SheldonPeters7/HomeOwl/Capstone Project Files/THE CODE/code integration without beeper.docx

#include <Wire.h>

#include <Adafruit_VL53L0X.h>

#include <IRremote.h>

/******************************* Pin Definitions ********************************/

// ToF XSHUT Pins

#define XSHUT_FAR_RIGHT 4

#define XSHUT_MID_RIGHT 5

#define XSHUT_MID_LEFT 6

#define XSHUT_FAR_LEFT 7

// Motor Control

const int leftencoderApin = 2;

const int leftencoderBpin = 3;

const int rightencoderApin = 18;

const int rightencoderBpin = 19;

const int leftdirpin = 11;

const int rightdirpin = 12;

const int leftpwmpin = 9;

const int rightpwmpin = 10;

// IR & LEDs

#define RED 30

#define GREEN 31

#define BLUE 32

const int receiver = 8; // IR receiver pin

// Sound & Motion

const int sensorAnalogPin = A0;

const int sensorDigitalPin = 28;

const int ledPin = LED_BUILTIN;

const int pirPin1 = 22;

const int pirPin2 = 23;

const int pirPin3 = 24;

const int pirPin4 = 25;

/***************************** Sensor Objects ***********************************/

Adafruit_VL53L0X loxFarRight = Adafruit_VL53L0X();

Adafruit_VL53L0X loxMidRight = Adafruit_VL53L0X();

Adafruit_VL53L0X loxMidLeft = Adafruit_VL53L0X();

Adafruit_VL53L0X loxFarLeft = Adafruit_VL53L0X();

IRrecv irrecv(receiver);

/***************************** Global Variables *********************************/

// MPU-9250 Configuration

const int MPU_ADDR = 0x68;

const float GYRO_SCALE = 131.0; // ±250°/s range

float yaw = 0;

float gyroZOffset = 0;

unsigned long prevTime = 0;

// Motor Control

int leftencoderpulse = 0;

int rightencoderpulse = 0;

double ipr = 18.85; // inches per revolution

double tpr = 900; // ticks per revolution

int targetangle = 0;

int pwm = 100;

double error = 0, eI = 0, eD = 0, prev_error = 0;

const float Kp = 1.2, Ki = 0.3, Kd = 0;

float omega = 0, vL = 0, vR = 0;

const float wheelbase = 13.7; // inches

// System State

int ROBOT_STATE = 0; // 0=Off, 1=Standby, 2=Moving, 3=Searching

unsigned long stateStartTime = 0;

#define STANDBY_DURATION 3000

#define MOVING_DURATION 5000

#define SEARCHING_DURATION 5000

// Timing Intervals

unsigned long lastToFRead = 0;

unsigned long lastYawPrint = 0;

unsigned long lastNoiseTime = 0;

unsigned long lastMotionTime = 0;

const unsigned long yawPrintInterval = 1000;

const unsigned long noiseCooldown = 1000;

const unsigned long motionCooldown = 1000;

/********************************* Setup ***************************************/

void setup() {

Serial.begin(115200);

Wire.begin();

// Initialize MPU

Wire.beginTransmission(MPU_ADDR);

Wire.write(0x6B); // PWR_MGMT_1

Wire.write(0); // Wake up

Wire.endTransmission();

calibrateGyro();

// Initialize ToF sensors

pinMode(XSHUT_FAR_RIGHT, OUTPUT);

pinMode(XSHUT_MID_RIGHT, OUTPUT);

pinMode(XSHUT_MID_LEFT, OUTPUT);

pinMode(XSHUT_FAR_LEFT, OUTPUT);

initializeSensor(loxFarRight, XSHUT_FAR_RIGHT, 0x30, "Far Right");

initializeSensor(loxMidRight, XSHUT_MID_RIGHT, 0x31, "Middle Right");

initializeSensor(loxMidLeft, XSHUT_MID_LEFT, 0x32, "Middle Left");

initializeSensor(loxFarLeft, XSHUT_FAR_LEFT, 0x33, "Far Left");

// Motor Control Initialization

pinMode(leftencoderApin, INPUT);

pinMode(leftencoderBpin, INPUT);

attachInterrupt(digitalPinToInterrupt(leftencoderApin), ALeadingLeft, RISING);

attachInterrupt(digitalPinToInterrupt(leftencoderBpin), BLeadingLeft, RISING);

attachInterrupt(digitalPinToInterrupt(rightencoderApin), ALeadingRight, RISING);

attachInterrupt(digitalPinToInterrupt(rightencoderBpin), BLeadingRight, RISING);

pinMode(leftdirpin, OUTPUT);

pinMode(rightdirpin, OUTPUT);

pinMode(leftpwmpin, OUTPUT);

pinMode(rightpwmpin, OUTPUT);

// IR & LED Initialization

pinMode(RED, OUTPUT);

pinMode(GREEN, OUTPUT);

pinMode(BLUE, OUTPUT);

setLedState(0);

irrecv.enableIRIn();

// Sound & Motion Initialization

pinMode(sensorDigitalPin, INPUT);

pinMode(ledPin, OUTPUT);

pinMode(pirPin1, INPUT);

pinMode(pirPin2, INPUT);

pinMode(pirPin3, INPUT);

pinMode(pirPin4, INPUT);

calibrateSensor();

Serial.println("System initialization complete!");

delay(2000); // Initial stabilization

}

/********************************* Main Loop ***********************************/

void loop() {

// Update sensor data

updateGyro();

checkSound();

checkMotion();

// Handle IR input

if (irrecv.decode()) {

translateIR();

irrecv.resume();

}

// State machine processing

processStateMachine();

// Handle periodic tasks

printYawIfNeeded();

readToFSensorsPeriodically();

}

/***************************** Core Functions **********************************/

void processStateMachine() {

if (ROBOT_STATE == 0) return;

unsigned long currentTime = millis();

unsigned long elapsedTime = currentTime - stateStartTime;

switch (ROBOT_STATE) {

case 1: // Standby

if (elapsedTime >= STANDBY_DURATION) {

setState(2);

}

break;

case 2: // Moving

computePID();

rotateRobotRight();

if (elapsedTime >= MOVING_DURATION) {

setState(3);

}

break;

case 3: // Searching

if (elapsedTime >= SEARCHING_DURATION) {

setState(2);

}

break;

}

}

void setState(int newState) {

ROBOT_STATE = newState;

stateStartTime = millis();

setLedState(ROBOT_STATE);

Serial.print("New state: ");

Serial.println(ROBOT_STATE);

}

/***************************** ToF Functions ***********************************/

void initializeSensor(Adafruit_VL53L0X &sensor, int xshutPin, uint8_t newAddress, const char* position) {

digitalWrite(xshutPin, LOW);

delay(10);

digitalWrite(xshutPin, HIGH);

delay(10);

if (!sensor.begin(newAddress)) {

Serial.print(position);

Serial.println(" sensor failed to boot!");

while(1);

}

Serial.print(position);

Serial.print(" sensor initialized at 0x");

Serial.println(newAddress, HEX);

}

void readSensor(Adafruit_VL53L0X &sensor, const char* position) {

VL53L0X_RangingMeasurementData_t measure;

sensor.rangingTest(&measure, false);

if(measure.RangeStatus != 4) {

Serial.print(position);

Serial.print(": ");

Serial.print(measure.RangeMilliMeter);

Serial.println(" mm");

} else {

Serial.print(position);

Serial.println(": Out of range");

}

}

void readAllToFSensors() {

readSensor(loxFarRight, "Far Right");

readSensor(loxMidRight, "Middle Right");

readSensor(loxMidLeft, "Middle Left");

readSensor(loxFarLeft, "Far Left");

}

void readToFSensorsPeriodically() {

if (millis() - lastToFRead >= 1000) {

readAllToFSensors();

lastToFRead = millis();

}

}

/***************************** MPU Functions ***********************************/

void updateGyro() {

int16_t rawGyroZ = readGyroZ();

float gyroZ = (rawGyroZ - gyroZOffset) / GYRO_SCALE;

unsigned long currentTime = micros();

float dt = (currentTime - prevTime) / 1000000.0;

prevTime = currentTime;

yaw += gyroZ * dt;

}

void printYawIfNeeded() {

if (millis() - lastYawPrint >= yawPrintInterval) {

Serial.print("Yaw: ");

Serial.println(yaw, 2);

lastYawPrint = millis();

}

}

void calibrateGyro() {

Serial.println("Calibrating gyro... Keep sensor stationary!");

delay(1000);

long total = 0;

for(int i = 0; i < 1000; i++) {

total += readGyroZ();

delay(1);

}

gyroZOffset = total / 1000.0;

Serial.print("Calibration offset: ");

Serial.println(gyroZOffset);

}

int16_t readGyroZ() {

Wire.beginTransmission(MPU_ADDR);

Wire.write(0x47); // GYRO_ZOUT_H

Wire.endTransmission(false);

Wire.requestFrom(MPU_ADDR, 2, true);

return Wire.read() << 8 | Wire.read();

}

/*************************** Sound/Motion Functions ****************************/

void calibrateSensor() {

long sum = 0;

for(int i = 0; i < 50; i++) sum += analogRead(sensorAnalogPin);

quietLevel = sum / 50;

loudNoiseThreshold = 400; // Hard-coded for testing

Serial.println("Sound sensor calibrated");

}

void checkSound() {

int analogValue = analogRead(sensorAnalogPin);

int digitalValue = digitalRead(sensorDigitalPin);

if((analogValue > loudNoiseThreshold) && (digitalValue == HIGH) &&

(millis() - lastNoiseTime > noiseCooldown)) {

handleNoiseDetection(analogValue);

triggerActionSound();

}

}

void handleNoiseDetection(int noiseLevel) {

lastNoiseTime = millis();

Serial.print("LOUD NOISE! Level: ");

Serial.println(noiseLevel);

for(int i = 0; i < 3; i++) {

digitalWrite(ledPin, HIGH);

delay(100);

digitalWrite(ledPin, LOW);

delay(100);

}

}

void triggerActionSound() {

Serial.println("Action: Sound detected!");

}

void checkMotion() {

if((digitalRead(pirPin1) || digitalRead(pirPin2) ||

digitalRead(pirPin3) || digitalRead(pirPin4)) &&

(millis() - lastMotionTime > motionCooldown)) {

handleMotionDetection();

}

}

void handleMotionDetection() {

lastMotionTime = millis();

Serial.println("Motion detected");

}

/***************************** Motor Functions *********************************/

void stopMotors() {

digitalWrite(leftdirpin, HIGH);

digitalWrite(rightdirpin, LOW);

analogWrite(leftpwmpin, 255);

analogWrite(rightpwmpin, 0);

}

// Encoder ISRs

void ALeadingLeft() {

if(digitalRead(leftencoderBpin) == LOW) leftencoderpulse--;

else leftencoderpulse++;

}

void BLeadingLeft() {

if(digitalRead(leftencoderApin) == LOW) leftencoderpulse++;

else leftencoderpulse--;

}

void ALeadingRight() {

if(digitalRead(rightencoderBpin) == LOW) rightencoderpulse++;

else rightencoderpulse--;

}

void BLeadingRight() {

if(digitalRead(rightencoderApin) == LOW) rightencoderpulse--;

else rightencoderpulse++;

}

void computePID() {

error = targetangle - yaw;

eI += error;

eD = prev_error - error;

prev_error = error;

if (eI > 200) eI = 0; // Anti-windup

omega = Kp * error + Ki * eI + Kd * eD;

omega = constrain(omega, 0, 100); // Limit output

}

void rotateRobotRight() {

vL = (omega * wheelbase) / 2;

vR = (omega * wheelbase) / 2;

if(targetangle > yaw) {

digitalWrite(leftdirpin, HIGH);

digitalWrite(rightdirpin, HIGH);

analogWrite(leftpwmpin, 255 - (vL * 0.152) - 45);

analogWrite(rightpwmpin, 255 - (vR * 0.152));

} else {

stopMotors();

}

}

/******************************* IR Functions **********************************/

void setLedState(int state) {

switch(state) {

case 0: // Off (Red)

digitalWrite(RED, HIGH); digitalWrite(GREEN, LOW); digitalWrite(BLUE, LOW);

break;

case 1: // Standby (Yellow)

digitalWrite(RED, HIGH); digitalWrite(GREEN, HIGH); digitalWrite(BLUE, LOW);

break;

case 2: // Moving (Green)

digitalWrite(RED, LOW); digitalWrite(GREEN, HIGH); digitalWrite(BLUE, LOW);

break;

case 3: // Searching (Cyan)

digitalWrite(RED, LOW); digitalWrite(GREEN, HIGH); digitalWrite(BLUE, HIGH);

break;

}

}

void translateIR() {

if (irrecv.decodedIRData.flags) {

irrecv.decodedIRData.decodedRawData = last_decodedRawData;

Serial.println("REPEAT!");

} else {

Serial.print("IR code:0x");

Serial.println(irrecv.decodedIRData.decodedRawData, HEX);

}

switch (irrecv.decodedIRData.decodedRawData) {

case 0xBA45FF00: // POWER

ROBOT_STATE = (ROBOT_STATE == 0) ? 1 : 0;

stateStartTime = millis();

setLedState(ROBOT_STATE);

break;

case 0xB847FF00: // FUNC/STOP

ROBOT_STATE = 1;

stateStartTime = millis();

setLedState(ROBOT_STATE);

break;

}

last_decodedRawData = irrecv.decodedIRData.decodedRawData;

delay(200);

}
