SheldonPeters7/HomeOwl/Capstone Project Files/THE CODE/IR-LED.docx

#include "IRremote.h"

// Define LED Pins

#define RED 30

#define GREEN 31

#define BLUE 32

int receiver = 8; // IR receiver pin

IRrecv irrecv(receiver);

uint32_t last_decodedRawData = 0;

int ROBOT_STATE = 0; // 0=Off, 1=Standby, 2=Moving, 3=Searching

unsigned long stateStartTime = 0;

void (*resetFunc)(void) = 0;

#define STANDBY_DURATION 3000

#define MOVING_DURATION 5000

#define SEARCHING_DURATION 5000

void setLedState(int state) {

switch(state) {

case 0: // Off (Red)

digitalWrite(RED, HIGH);

digitalWrite(GREEN, LOW);

digitalWrite(BLUE, LOW);

break;

case 1: // Standby (Yellow)

digitalWrite(RED, HIGH);

digitalWrite(GREEN, HIGH);

digitalWrite(BLUE, LOW);

break;

case 2: // Moving (Green)

digitalWrite(RED, LOW);

digitalWrite(GREEN, HIGH);

digitalWrite(BLUE, LOW);

break;

case 3: // Searching (Cyan)

digitalWrite(RED, LOW);

digitalWrite(GREEN, HIGH);

digitalWrite(BLUE, HIGH);

break;

}

}

void translateIR() {

if (irrecv.decodedIRData.flags) {

irrecv.decodedIRData.decodedRawData = last_decodedRawData;

Serial.println("REPEAT!");

} else {

Serial.print("IR code:0x");

Serial.println(irrecv.decodedIRData.decodedRawData, HEX);

}

switch (irrecv.decodedIRData.decodedRawData) {

case 0xBA45FF00: // POWER button

Serial.println("POWER");

if (ROBOT_STATE == 0) {

ROBOT_STATE = 1;

stateStartTime = millis();

setLedState(ROBOT_STATE);

} else {

ROBOT_STATE = 0;

setLedState(ROBOT_STATE);

}

Serial.print("New state: ");

Serial.println(ROBOT_STATE);

break;

case 0xB847FF00: // FUNC/STOP button (REPLACE THIS CODE WITH YOUR ACTUAL BUTTON'S HEX CODE)

Serial.println("FUNC/STOP");

ROBOT_STATE = 1; // Force standby state

stateStartTime = millis(); // Reset timer

setLedState(ROBOT_STATE);

Serial.print("New state: ");

Serial.println(ROBOT_STATE);

break;

default:

Serial.println("Unknown button");

}

last_decodedRawData = irrecv.decodedIRData.decodedRawData;

delay(200);

}

void setup() {

Serial.begin(9600);

pinMode(RED, OUTPUT);

pinMode(GREEN, OUTPUT);

pinMode(BLUE, OUTPUT);

setLedState(0);

Serial.println("IR Robot State Controller");

irrecv.enableIRIn();

}

void loop() {

if (irrecv.decode()) {

translateIR();

irrecv.resume();

}

if (ROBOT_STATE != 0) {

unsigned long currentTime = millis();

unsigned long elapsedTime = currentTime - stateStartTime;

switch (ROBOT_STATE) {

case 1: // Standby

if (elapsedTime >= STANDBY_DURATION) {

ROBOT_STATE = 2;

stateStartTime = currentTime;

setLedState(ROBOT_STATE);

Serial.print("New state: ");

Serial.println(ROBOT_STATE);

}

break;

case 2: // Moving

if (elapsedTime >= MOVING_DURATION) {

ROBOT_STATE = 3;

stateStartTime = currentTime;

setLedState(ROBOT_STATE);

Serial.print("New state: ");

Serial.println(ROBOT_STATE);

}

break;

case 3: // Searching

if (elapsedTime >= SEARCHING_DURATION) {

ROBOT_STATE = 2;

stateStartTime = currentTime;

setLedState(ROBOT_STATE);

Serial.print("New state: ");

Serial.println(ROBOT_STATE);

}

break;

}

}

}
