SheldonPeters7/HomeOwl/Capstone Project Files/Capstone Prep Work/Progress Presentations - Capstone Prep/prep Progress Presentation 2.pptx

## Home Owl Autonomous Security Robot

Samantha Buckle
Dylan Dauz
Sameeh Olipani
Sheldon Peters

## Project Recap

- This project aims to design and build a robot for use in the monitoring of indoor spaces
- Robot will be capable of:
  - Autonomous movement
  - Navigation of a building or room without the need for human control
  - Utilize sensors to detect loud noises or the presence of a person
  - Flash lights and play an alarm sound when disturbance is detected
  - Get signal from remote control to turn the system on and off

## Parts list

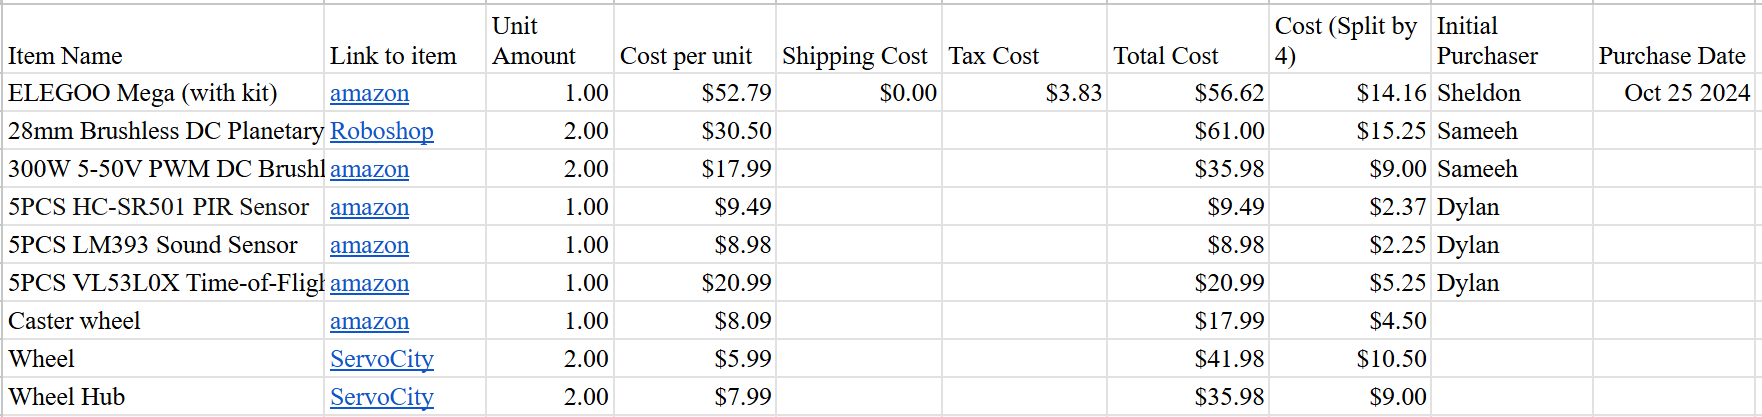
[picture p16: figure]

## Concept Design

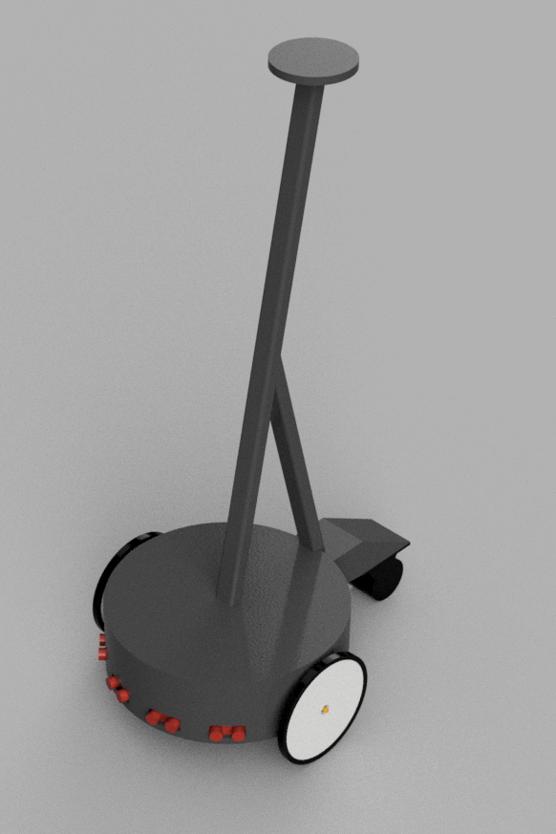
[picture p17: figure]

## Concept Design

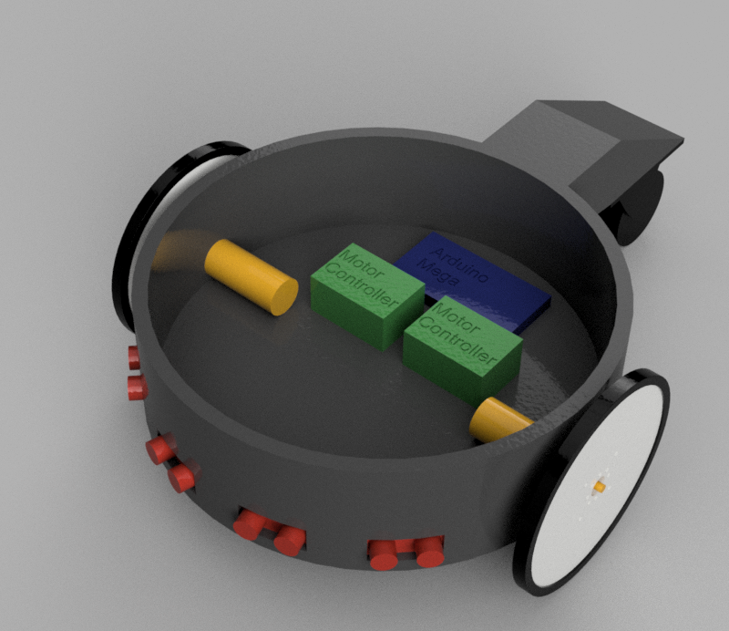
[picture p18: figure]

## Next Steps

- Order parts
- Safety trainings for lab access / 3D printing access
- Refine / finalize design
