SheldonPeters7/HomeOwl/Capstone Project Files/Fusion 360 files/Capstone 3D Models/Capstone/Rough Draft 2/Wheel.stl

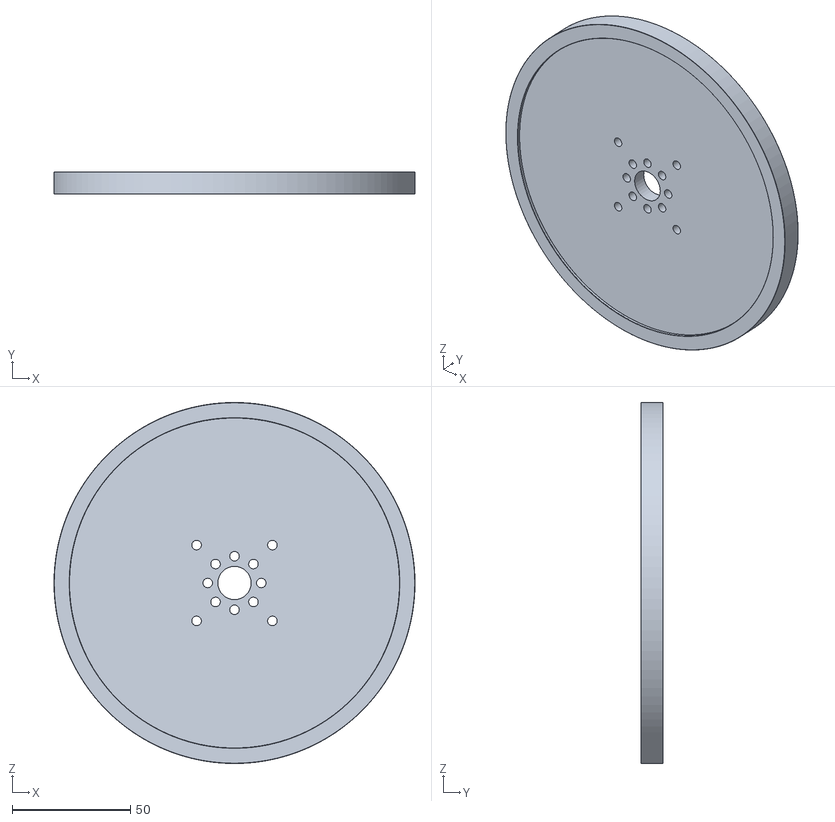
[picture p49: CAD file, 2025-04-22]
Capstone Project Files/Fusion 360 files/Capstone 3D Models/Capstone/Rough Draft 2/Wheel.stl
152.4 x 9.35 x 152.4
