SheldonPeters7/HomeOwl/Capstone Project Files/Fusion 360 files/Capstone 3D Models/Capstone/Rough Draft 2/Caster Wheel.stl

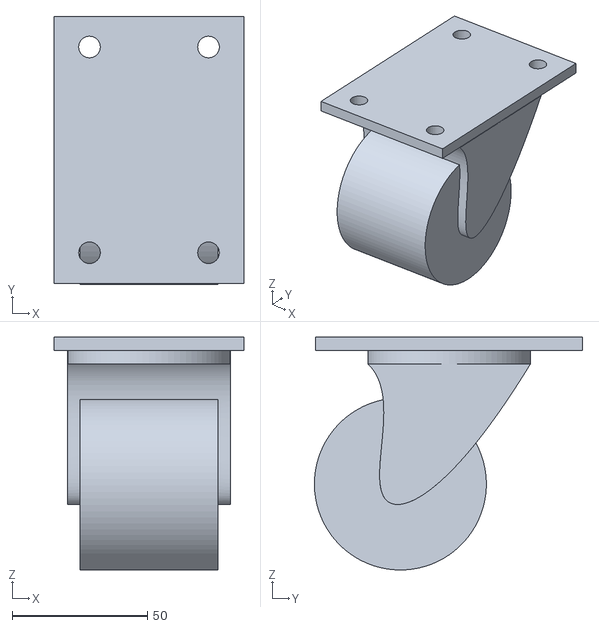
[picture p50: CAD file, 2025-04-22]
Capstone Project Files/Fusion 360 files/Capstone 3D Models/Capstone/Rough Draft 2/Caster Wheel.stl
70.1 x 99.0 x 86.0
