SheldonPeters7/HomeOwl/Capstone Project Files/Fusion 360 files/Capstone 3D Models/Capstone/Prototype/Arduino Mega Mount Plate.stl

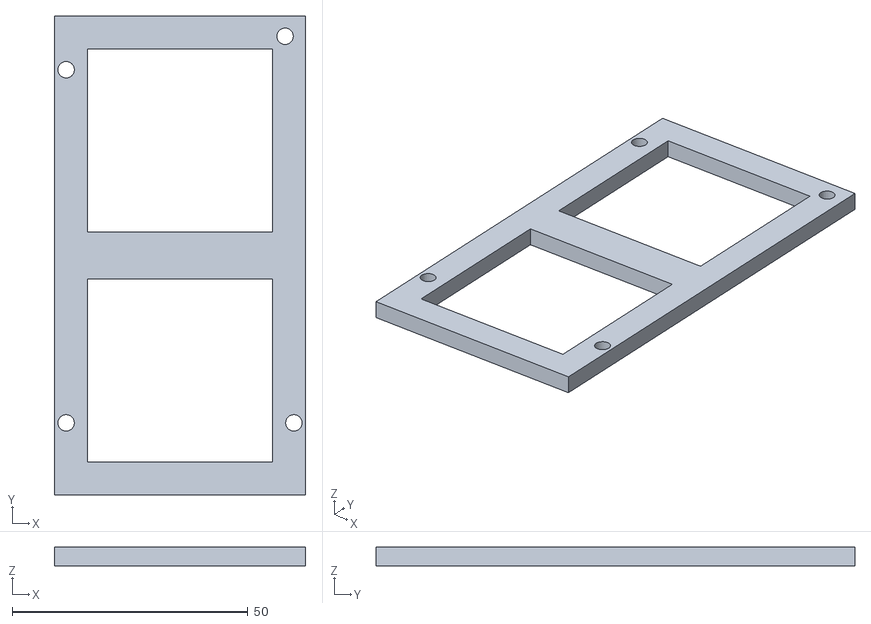
[picture p51: CAD file, 2025-04-22]
Capstone Project Files/Fusion 360 files/Capstone 3D Models/Capstone/Prototype/Arduino Mega Mount Plate.stl
53.3 x 101.6 x 4.00
