SheldonPeters7/HomeOwl/Capstone Project Files/Fusion 360 files/Capstone 3D Models/Capstone/Rough Draft 2/DC Brushless Motor.stl

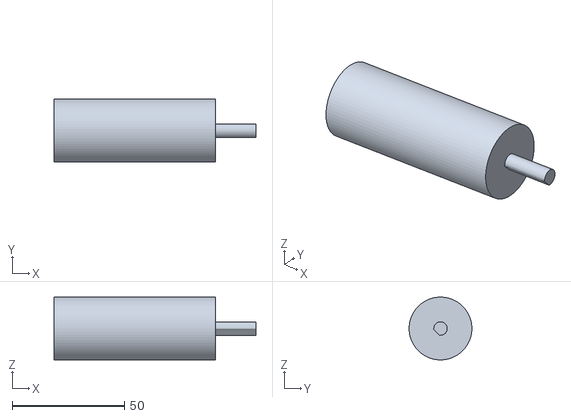
[picture p52: CAD file, 2025-04-22]
Capstone Project Files/Fusion 360 files/Capstone 3D Models/Capstone/Rough Draft 2/DC Brushless Motor.stl
90.0 x 28.0 x 28.0
