SheldonPeters7/HomeOwl/Capstone Project Files/Fusion 360 files/Capstone 3D Models/Capstone/Prototype/Encoder Asembly.stl

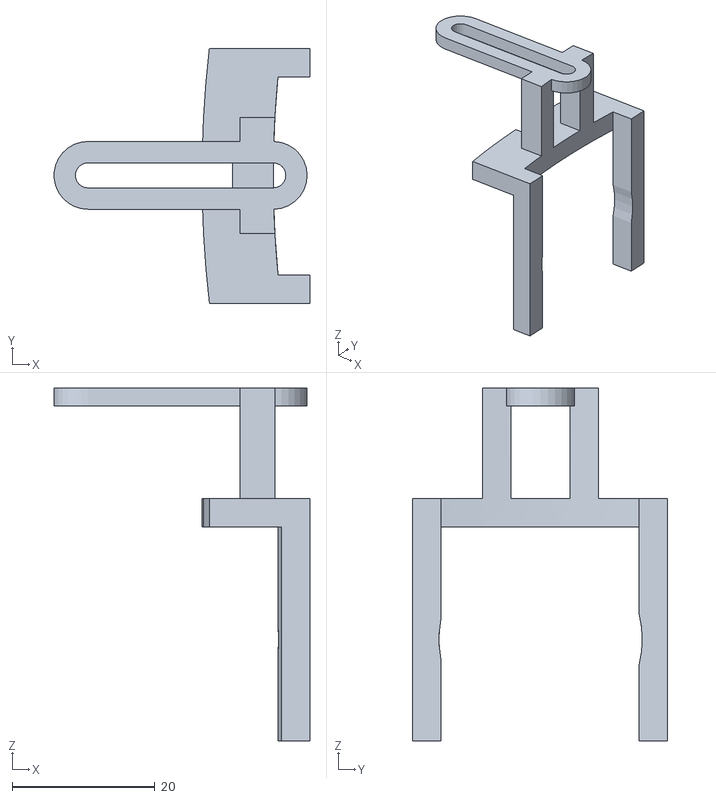
[picture p53: CAD file, 2025-04-22]
Capstone Project Files/Fusion 360 files/Capstone 3D Models/Capstone/Prototype/Encoder Asembly.stl
35.8 x 35.8 x 49.5
