SheldonPeters7/HomeOwl/Capstone Project Files/Fusion 360 files/Capstone 3D Models/Capstone/Rough Draft 2/Ultrasonic Sensor Place Holder.stl

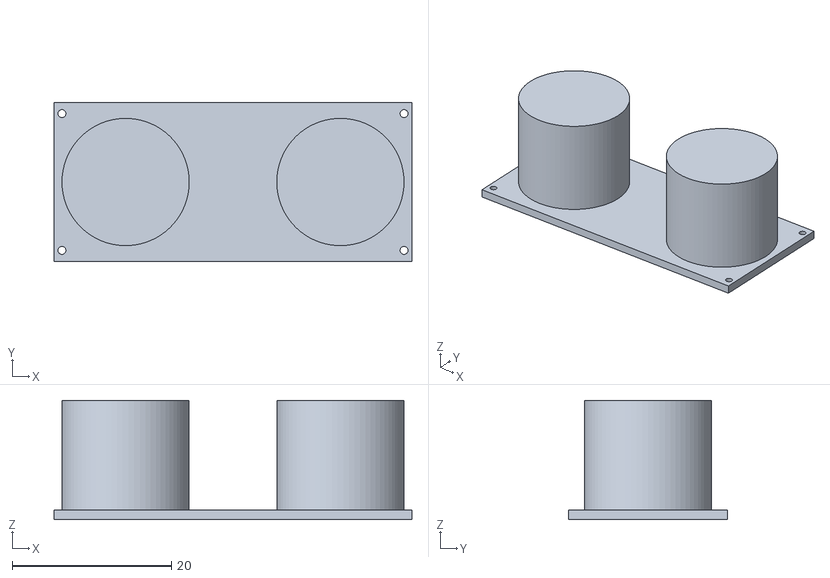
[picture p54: CAD file, 2025-04-22]
Capstone Project Files/Fusion 360 files/Capstone 3D Models/Capstone/Rough Draft 2/Ultrasonic Sensor Place Holder.stl
45.0 x 20.0 x 15.0
