SheldonPeters7/HomeOwl/Capstone Project Files/Fusion 360 files/Capstone 3D Models/Capstone/Prototype/Prototype Base with Motor Mount Converter.stl

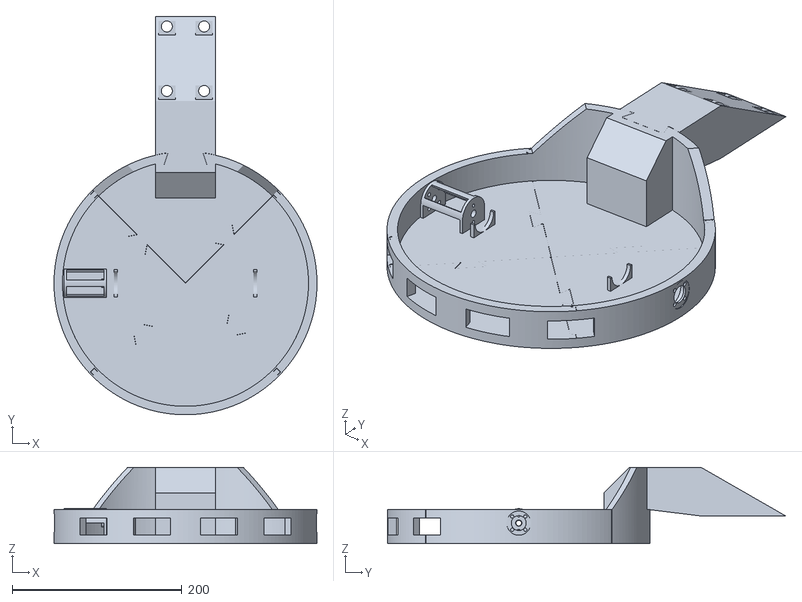
[picture p55: CAD file, 2025-04-22]
Capstone Project Files/Fusion 360 files/Capstone 3D Models/Capstone/Prototype/Prototype Base with Motor Mount Converter.stl
310.0 x 469.6 x 90.0
