SheldonPeters7/HomeOwl/Capstone Project Files/Fusion 360 files/Capstone 3D Models/Capstone/Prototype/Right Slice.stl

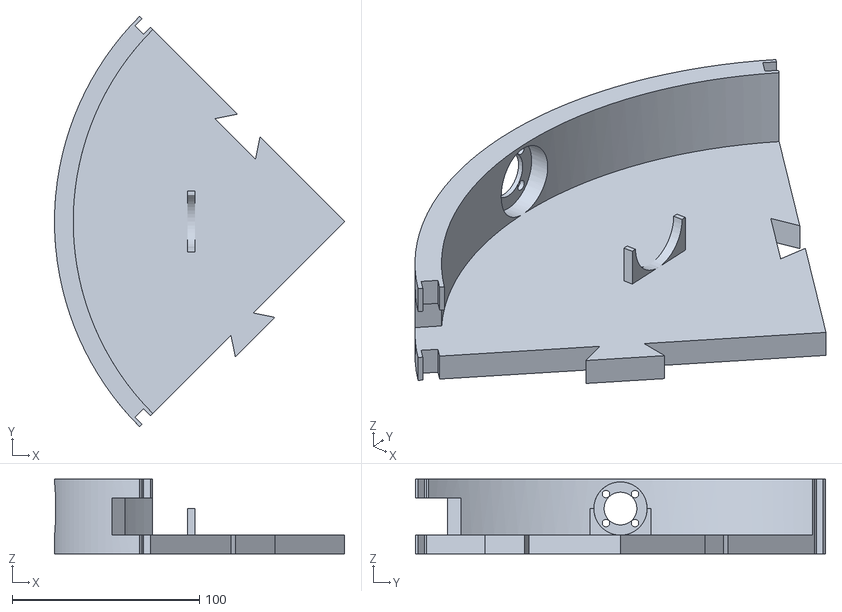
[picture p56: CAD file, 2025-04-22]
Capstone Project Files/Fusion 360 files/Capstone 3D Models/Capstone/Prototype/Right Slice.stl
155.0 x 219.2 x 40.0
