SheldonPeters7/HomeOwl/Capstone Project Files/Fusion 360 files/Capstone 3D Models/Capstone/Rough Draft 2/Base.stl

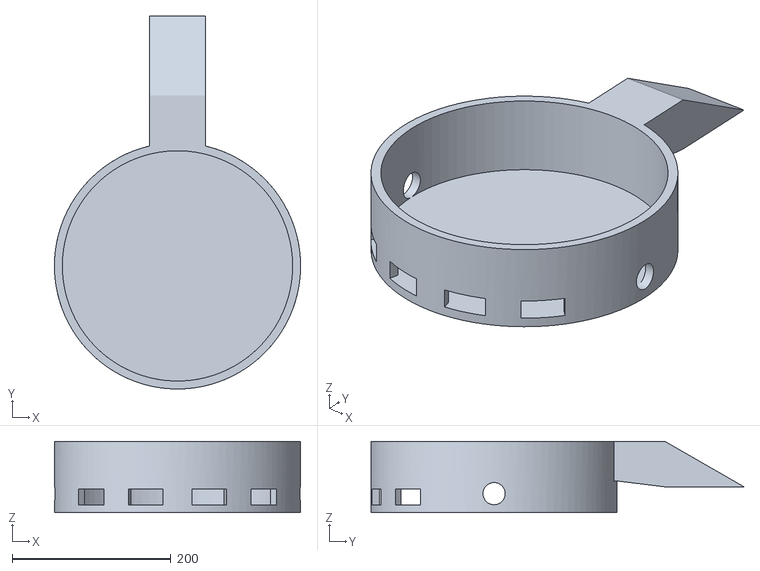
[picture p57: CAD file, 2025-04-22]
Capstone Project Files/Fusion 360 files/Capstone 3D Models/Capstone/Rough Draft 2/Base.stl
310.0 x 469.7 x 90.0
