SheldonPeters7/HomeOwl/Capstone Project Files/Fusion 360 files/Capstone 3D Models/Capstone/Prototype/Motor Controller Base Plate.stl

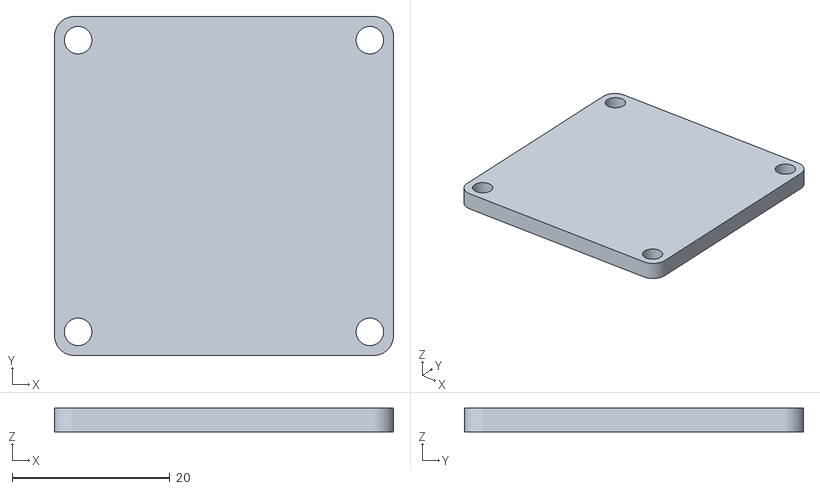
[picture p58: CAD file, 2025-04-22]
Capstone Project Files/Fusion 360 files/Capstone 3D Models/Capstone/Prototype/Motor Controller Base Plate.stl
43.0 x 43.0 x 3.00
