SheldonPeters7/HomeOwl/Capstone Project Files/THE CODE/Old Test Code/(old) main code.docx

#include<Wire.h>

// Pin definitions

const int left_pwmPin = 11; // PWM pin for speed control (Blue)

const int right_pwmPin = 9;

const int left_dirPin = 10; // Digital pin for direction control (White)

const int right_dirPin = 8;

unsigned long offset = 1999;

// PWM speeds

int pwm_left = 0;

int pwm_right = 0;

void setup()

{

// Initialize serial communication for debugging

Serial.begin(9600);

// Set pin modes

pinMode(left_pwmPin, OUTPUT);

pinMode(right_pwmPin, OUTPUT);

pinMode(left_dirPin, OUTPUT);

pinMode(right_dirPin, OUTPUT);

digitalWrite(left_dirPin, HIGH);

digitalWrite(right_dirPin, LOW);

analogWrite(left_pwmPin, 255);

analogWrite(right_pwmPin, 255);

// open serial monitor

delay(2000);

}

// to go forward, left_dirPin is HIGH, right_dirPin is LOW

void loop()

{

// Example: Drive robot forward

digitalWrite(left_dirPin, HIGH);

digitalWrite(right_dirPin, LOW);

unsigned long clock = millis();

//Serial.println(clock);

if (clock > offset + 5000)

{

pwm_left = 0;

pwm_right = 0;

} else {

pwm_left = 50;

pwm_right = 50;

}

analogWrite(left_pwmPin, 255 - pwm_left);

analogWrite(right_pwmPin, 255 - pwm_right);

delay(500);

}
