SheldonPeters7/HomeOwl/Capstone Project Files/THE CODE/Old Test Code/main code w endoders and pid.docx

// Pin definitions

const int left_pwmPin = 11; // PWM pin for speed control (Blue)

const int right_pwmPin = 9;

const int left_dirPin = 10; // Digital pin for direction control (White)

const int right_dirPin = 8;

const int left_opticPin = 3; // FG signal input for speed measurement (Yellow)

const int right_opticPin = 2;

////////////////////////////////////////

// Variables for speed measurement

volatile int left_pulseCount = 0; // Counter for FG pulses

volatile int right_pulseCount = 0; // Counter for FG pulses

unsigned long lastTime = 0; // Time of last RPM calculation

// PWM speeds

int pwm_left = 0;

int pwm_right = 0;

// RPM

int tpr = 20; // ticks per rotation

// PID VARIABLES

// double Ep, Ei, Ed = 0; // P, I, D errors

// double kp, ki, kd;

// double dt, prev_time, current_time;

// double setpoint, actual;

// double pid_output;

// double curr_error, prev_error;

// double error = setpoint - actual;

unsigned long offset = 1999;

void setup()

{

// Initialize serial communication for debugging

Serial.begin(9600);

// Set pin modes

pinMode(left_pwmPin, OUTPUT);

pinMode(right_pwmPin, OUTPUT);

pinMode(left_dirPin, OUTPUT);

pinMode(right_dirPin, OUTPUT);

pinMode(left_opticPin, INPUT);

pinMode(right_opticPin, INPUT);

// Attach interrupt to FG pin for pulse

attachInterrupt(digitalPinToInterrupt(right_opticPin), RpulseCount, RISING);

attachInterrupt(digitalPinToInterrupt(left_opticPin), LpulseCount, RISING);

prev_time = 0;

kp = 0;

ki = 0;

kd = 0;

digitalWrite(left_dirPin, HIGH);

digitalWrite(right_dirPin, LOW);

analogWrite(left_pwmPin, 255);

analogWrite(right_pwmPin, 255);

delay(2000);

}

// to go forward, left_dirPin is HIGH, right_dirPin is LOW

void loop()

{

// Example: Drive robot forward

digitalWrite(left_dirPin, HIGH);

digitalWrite(right_dirPin, LOW);

unsigned long clock = millis();

Serial.println(clock);

if (clock > offset + 3000)

{

pwm_left = 0;

pwm_right = 0;

} else {

pwm_left = 50;

pwm_right = 50;

}

analogWrite(left_pwmPin, 255 - pwm_left);

analogWrite(right_pwmPin, 255 - pwm_right);

delay(500);

Serial.print("left pulse: ");

Serial.println(left_pulseCount);

Serial.print("right pulse: ");

Serial.println(right_pulseCount);

//Serial.println(temptime);

/////////////////// PID STUFFSSSSSSSSSSSSSSSS /////

// current_time = millis();

// dt = (current_time - prev_time) / 1000; // puts in seconds

// prev_time = current_time;

// actual = map(analogRead(///pwmPIN L and R motor??///), 0,1023, 255,0);

// analogWrite(motor, pwm value);

// curr_error = setpoint - actual;

// pid_output = pid(curr_error);

}

void LpulseCount()

{

if(digitalRead(left_opticPin) == HIGH)

{

left_pulseCount++;

}

else

{

left_pulseCount--;

}

}

void RpulseCount()

{

if(digitalRead(right_opticPin) == HIGH)

{

right_pulseCount++;

}

else

{

right_pulseCount--;

}

}

/////////////////////////////////

//void setMotor(int direction, int pwm_val)

// double pid(double error)

// {

// Ep = error;

// Ei += error * dt; //double check this one is it +=????

// Ed = (error - prev_error) / dt; //DOUBLE CHECK!!!!!!!!!!!!!!!!

// prev_error = error;

// motorpwm = (kp * Ep) + (ki * Ei) + (kd * Ed);

// }
