SheldonPeters7/HomeOwl/Capstone Project Files/THE CODE/Old Test Code/sound and motion 4 PIR.docx

/* SOUND SENSOR SETTINGS */

const int sensorAnalogPin = A0; // Analog input

const int sensorDigitalPin = 28; // Digital input D28

const int ledPin = LED_BUILTIN; // Built-in LED

// Sound detection settings

unsigned long lastNoiseTime = 0;

const unsigned long noiseCooldown = 1000; // 1-second cooldown

int loudNoiseThreshold; // Set during calibration

int quietLevel; // Ambient noise baseline

/* PIR SENSOR SETTINGS */

// PIR Sensor Pins (Inputs)

int pirPin1 = 22; // HC-SR501 #1 on Pin 22

int pirPin2 = 23; // HC-SR501 #2 on Pin 23

int pirPin3 = 24; // HC-SR501 #3 on Pin 24

int pirPin4 = 25; // HC-SR501 #4 on Pin 25

// Motion detection settings

unsigned long lastMotionTime = 0;

const unsigned long motionCooldown = 1000; // 1-second cooldown

void setup() {

Serial.begin(9600);

// Sound sensor setup

pinMode(sensorDigitalPin, INPUT);

pinMode(ledPin, OUTPUT);

calibrateSensor();

// PIR sensors setup

pinMode(pirPin1, INPUT);

pinMode(pirPin2, INPUT);

pinMode(pirPin3, INPUT);

pinMode(pirPin4, INPUT);

Serial.println("Dual Sensor System Ready");

}

void loop() {

// Handle sound detection

int analogValue = analogRead(sensorAnalogPin);

int digitalValue = digitalRead(sensorDigitalPin);

if (isLoudNoise(analogValue, digitalValue)) {

handleNoiseDetection(analogValue);

triggerActionSound();

}

// Handle motion detection

checkMotionSensors();

delay(10); // Small delay for stability

}

/* SOUND SENSOR FUNCTIONS */

void calibrateSensor() {

// Calibration (50 samples)

long sum = 0;

for (int i = 0; i < 50; i++) {

sum += analogRead(sensorAnalogPin);

}

quietLevel = sum / 50;

loudNoiseThreshold = quietLevel + 100; // Threshold 100 above ambient

//more calibration may be needed

loudNoiseThreshold = 400;

//currently hard coded for testing sensitivty

}

bool isLoudNoise(int analogVal, int digitalVal) {

return (analogVal > loudNoiseThreshold) &&

(digitalVal == HIGH) &&

(millis() - lastNoiseTime > noiseCooldown);

}

void handleNoiseDetection(int noiseLevel) {

lastNoiseTime = millis();

Serial.print("LOUD NOISE! Level: ");

Serial.print(noiseLevel);

Serial.print(" (Threshold: ");

Serial.print(loudNoiseThreshold);

Serial.println(")");

// Visual feedback (3 blinks)

for (int i = 0; i < 3; i++) {

digitalWrite(ledPin, HIGH);

delay(100);

digitalWrite(ledPin, LOW);

delay(100);

}

}

void triggerActionSound() {

Serial.println("Custom action: Sound detected!"); // Placeholder code

}

/* MOTION SENSOR FUNCTIONS */

void checkMotionSensors() {

if ((digitalRead(pirPin1) || digitalRead(pirPin2) ||

digitalRead(pirPin3) || digitalRead(pirPin4)) &&

(millis() - lastMotionTime > motionCooldown)) {

handleMotionDetection();

}

}

void handleMotionDetection() {

lastMotionTime = millis();

Serial.println("Motion detected");

}
